kevinakasam/BFACH/Images/6.jpg

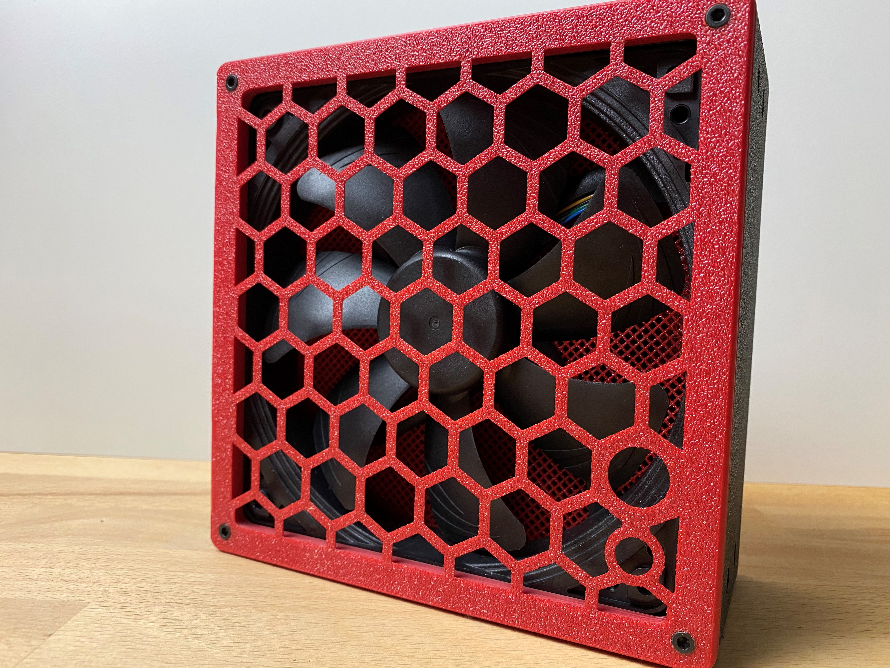
Images/6.jpg
