kevinakasam/BFACH/Images/7.jpg

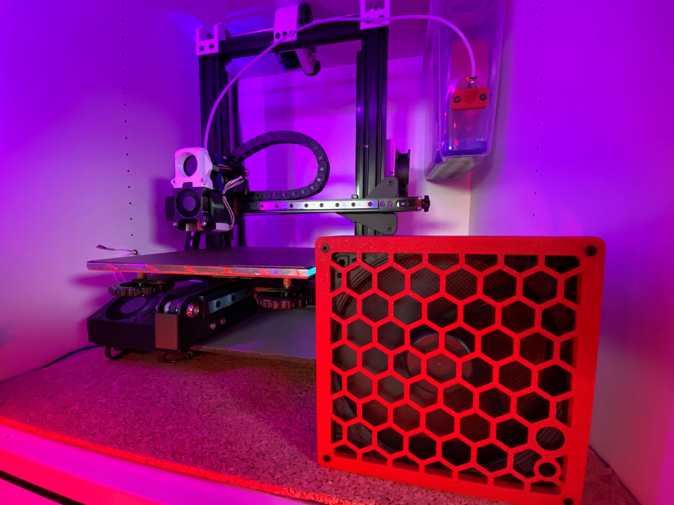
Images/7.jpg
